dchwebb/Kishoof/Graphics/Kishoof_Front2.jpg

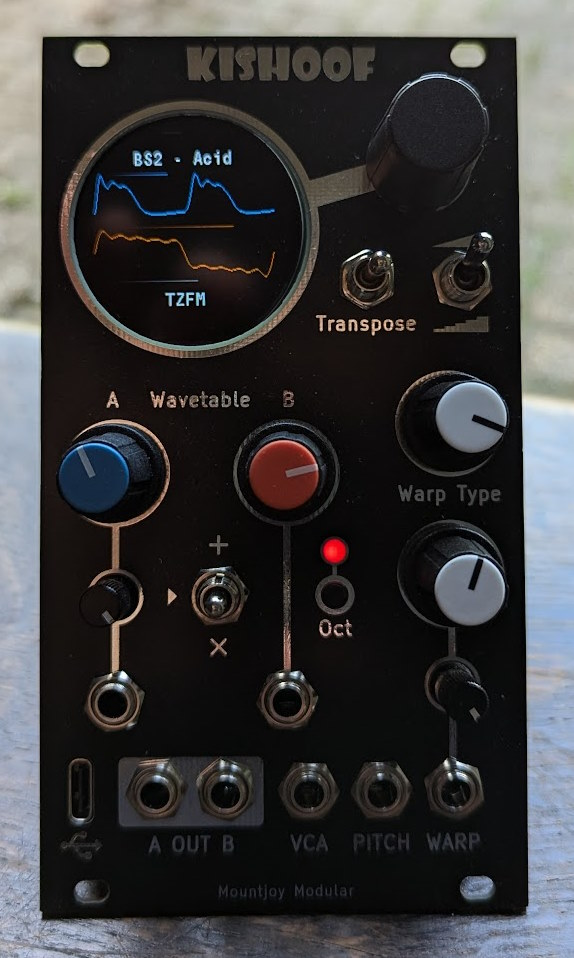
Graphics/Kishoof_Front2.jpg
