dchwebb/Kishoof/Kishoof/src/usb/USB.cpp

#include "USB.h"
#include "GpioPin.h"


USB usb;

extern "C" {
// To enable USB for printf commands (To print floats enable 'Use float with printf from newlib-nano' MCU Build Settings)
size_t _write(int handle, const unsigned char* buf, size_t bufSize)
{
	if (usb.devState == USB::DeviceState::Configured) {
		return usb.SendString(buf, bufSize);
	} else {
		return 0;
	}
}
}

// procedure to allow classes to pass configuration data back via endpoint 1 (eg CDC line setup, MSC MaxLUN etc)
void USB::EP0In(const uint8_t* buff, const uint32_t size)
{
	ep0.inBuffSize = std::min(size, static_cast<uint32_t>(req.Length));
	ep0.inBuff = buff;
	ep0State = EP0State::DataIn;

	USBUpdateDbg({}, {}, {}, ep0.inBuffSize, (uint32_t*)ep0.inBuff);

	EPStartXfer(Direction::in, 0, ep0.inBuffSize);		// sends blank request back
}


void USB::InterruptHandler()					// In Drivers\STM32H7xx_HAL_Driver\Src\stm32h7xx_hal_pcd.c
{
	uint32_t epnum, ep_intr, epint;

	// Handle spurious interrupt
	if ((USB_OTG_HS->GINTSTS & USB_OTG_HS->GINTMSK) == 0) {
		return;
	}

	///////////		10			RXFLVL: RxQLevel Interrupt:  Rx FIFO non-empty Indicates that there is at least one packet pending to be read from the Rx FIFO.
	if (ReadInterrupts(USB_OTG_GINTSTS_RXFLVL))	{
		USB_OTG_HS->GINTMSK &= ~USB_OTG_GINTSTS_RXFLVL;

		const uint32_t receiveStatus = USB_OTG_HS->GRXSTSP;		// OTG status read and pop register: not shown in SFR, but read only (ie do not pop) register under OTG_FS_GLOBAL->FS_GRXSTSR_Device
		epnum = receiveStatus & USB_OTG_GRXSTSP_EPNUM;			// Get the endpoint number
		const uint16_t packetSize = (receiveStatus & USB_OTG_GRXSTSP_BCNT) >> 4;

		USBUpdateDbg(receiveStatus, {}, epnum, packetSize, nullptr);

		if (((receiveStatus & USB_OTG_GRXSTSP_PKTSTS) >> 17) == OutDataReceived && packetSize != 0) {	// 2 = OUT data packet received
			ReadPacket(classByEP[epnum]->outBuff, packetSize, classByEP[epnum]->outBuffOffset);
			USBUpdateDbg({}, {}, {}, {}, classByEP[epnum]->outBuff + classByEP[epnum]->outBuffOffset);
			if (classByEP[epnum]->outBuffPackets > 1) {
				classByEP[epnum]->outBuffOffset += (packetSize / 4);			// When receiving multiple packets increase buffer offset (packet size in bytes -> 32 bit ints)
			}
		} else if (((receiveStatus & USB_OTG_GRXSTSP_PKTSTS) >> 17) == SetupDataReceived) {				// 6 = SETUP data packet received
			ReadPacket(classByEP[epnum]->outBuff, 8U, 0);
			USBUpdateDbg({}, {}, {}, {}, classByEP[epnum]->outBuff);
		} else if (((receiveStatus & USB_OTG_GRXSTSP_PKTSTS) >> 17) == OutTransferCompleted) {			// 3 = transfer completed
			classByEP[epnum]->outBuffOffset = 0;
		}
		if (packetSize != 0) {
			classByEP[epnum]->outBuffCount = packetSize;
		}
		USB_OTG_HS->GINTMSK |= USB_OTG_GINTSTS_RXFLVL;
	}


	/////////// 	80000 		OEPINT OUT endpoint interrupt
	if (ReadInterrupts(USB_OTG_GINTSTS_OEPINT)) {

		// Read the output endpoint interrupt register to ascertain which endpoint(s) fired an interrupt
		ep_intr = ((USBx_DEVICE->DAINT & USBx_DEVICE->DAINTMSK) & USB_OTG_DAINTMSK_OEPM_Msk) >> 16;

		// process each endpoint in turn incrementing the epnum and checking the interrupts (ep_intr) if that endpoint fired
		epnum = 0;
		while (ep_intr != 0) {
			if ((ep_intr & 1) != 0) {
				epint = USBx_OUTEP(epnum)->DOEPINT & USBx_DEVICE->DOEPMSK;

				USBUpdateDbg(epint, {}, epnum, {}, nullptr);

				if ((epint & USB_OTG_DOEPINT_XFRC) == USB_OTG_DOEPINT_XFRC) {		// 0x01 Transfer completed

					USBx_OUTEP(epnum)->DOEPINT = USB_OTG_DOEPINT_XFRC;				// Clear interrupt

					if (epnum == 0) {

						if (devState == DeviceState::Configured && classPendingData) {
							if ((req.RequestType & requestTypeMask) == RequestTypeClass) {
								// Previous OUT interrupt contains instruction (eg host sending CDC LineCoding); next command sends data (Eg LineCoding data)
								classesByInterface[req.Index]->ClassSetupData(req, (uint8_t*)ep0.outBuff);
							}
							classPendingData = false;
							EPStartXfer(Direction::in, 0, 0);
						}

						ep0State = EP0State::Idle;
						USBx_OUTEP(epnum)->DOEPCTL |= USB_OTG_DOEPCTL_STALL;
					} else {
						// Call appropriate data handler depending on endpoint of data
						if (classByEP[epnum]->outBuffPackets <= 1) {
							EPStartXfer(Direction::out, epnum, classByEP[epnum]->outBuffCount);
						}
						classByEP[epnum]->DataOut();
					}
				}

				if ((epint & USB_OTG_DOEPINT_STUP) == USB_OTG_DOEPINT_STUP) {		// SETUP phase done: the application can decode the received SETUP data packet.
					// Parse Setup Request containing data in outBuff filled by RXFLVL interrupt
					req.loadData((uint8_t*)classByEP[epnum]->outBuff);

					USBUpdateDbg({}, req, {}, {}, nullptr);

					ep0State = EP0State::Setup;

					switch (req.RequestType & 0x1F) {		// originally USBD_LL_SetupStage
					case RequestRecipientDevice:
						StdDevReq();
						break;

					case RequestRecipientInterface:
						if ((req.RequestType & requestTypeMask) == RequestTypeClass) {		// 0xA1 & 0x60 == 0x20

							// req.Index holds interface - locate which handler this relates to
							if (req.Length > 0) {
								classesByInterface[req.Index]->ClassSetup(req);
							} else {
								EPStartXfer(Direction::in, 0, 0);
							}
						}
						break;

					case RequestRecipientEndpoint:
						break;

					default:
						CtlError();
						break;
					}

					USBx_OUTEP(epnum)->DOEPINT = USB_OTG_DOEPINT_STUP;				// Clear interrupt
				}

				if ((epint & USB_OTG_DOEPINT_OTEPDIS) == USB_OTG_DOEPINT_OTEPDIS) {	// OUT token received when endpoint disabled
					USBx_OUTEP(epnum)->DOEPINT = USB_OTG_DOEPINT_OTEPDIS;			// Clear interrupt
				}
				if ((epint & USB_OTG_DOEPINT_OTEPSPR) == USB_OTG_DOEPINT_OTEPSPR) {	// Status Phase Received interrupt
					USBx_OUTEP(epnum)->DOEPINT = USB_OTG_DOEPINT_OTEPSPR;			// Clear interrupt
				}
				if ((epint & USB_OTG_DOEPINT_NAK) == USB_OTG_DOEPINT_NAK) {			// 0x2000 OUT NAK interrupt
					USBx_OUTEP(epnum)->DOEPINT = USB_OTG_DOEPINT_NAK;				// Clear interrupt
				}
			}
			epnum++;
			ep_intr >>= 1U;
		}

	}

	///////////		40000 		IEPINT: IN endpoint interrupt
	if (ReadInterrupts(USB_OTG_GINTSTS_IEPINT)) {

		// Read in the device interrupt bits [initially 1]
		ep_intr = (USBx_DEVICE->DAINT & USBx_DEVICE->DAINTMSK) & USB_OTG_DAINTMSK_IEPM_Msk;

		// process each endpoint in turn incrementing the epnum and checking the interrupts (ep_intr) if that endpoint fired
		epnum = 0;
		while (ep_intr != 0) {
			if ((ep_intr & 1) != 0) {

				epint = USBx_INEP(epnum)->DIEPINT & (USBx_DEVICE->DIEPMSK | (((USBx_DEVICE->DIEPEMPMSK >> (epnum & epAddressMask)) & 0x1U) << 7));

				USBUpdateDbg(epint, {}, epnum, {}, nullptr);

				if ((epint & USB_OTG_DIEPINT_XFRC) == USB_OTG_DIEPINT_XFRC) {			// 0x1 Transfer completed interrupt
					uint32_t fifoemptymsk = (0x1UL << (epnum & epAddressMask));
					USBx_DEVICE->DIEPEMPMSK &= ~fifoemptymsk;

					USBx_INEP(epnum)->DIEPINT = USB_OTG_DIEPINT_XFRC;

					if (epnum == 0) {
						if (ep0State == EP0State::DataIn && ep0.inBuffRem == 0) {
							ep0State = EP0State::StatusOut;								// After completing transmission on EP0 send an out packet [HAL_PCD_EP_Receive]
							EPStartXfer(Direction::out, 0, ep_maxPacket);

						} else if (ep0State == EP0State::DataIn && ep0.inBuffRem > 0) {		// For EP0 long packets are sent separately rather than streamed out of the FIFO
							ep0.inBuffSize = ep0.inBuffRem;
							ep0.inBuffRem = 0;
							USBUpdateDbg({}, {}, {}, ep0.inBuffSize, (uint32_t*)ep0.inBuff);

							EPStartXfer(Direction::in, 0, ep0.inBuffSize);
						}
					} else {
						classByEP[epnum]->DataIn();
						classByEP[epnum]->transmitting = false;
					}
				}

				if ((epint & USB_OTG_DIEPINT_TXFE) == USB_OTG_DIEPINT_TXFE) {			// 0x80 Transmit FIFO empty
					USBUpdateDbg({}, {}, {}, classByEP[epnum]->inBuffSize, (uint32_t*)classByEP[epnum]->inBuff);

					if (epnum == 0) {
						if (ep0.inBuffSize > ep_maxPacket) {
							ep0.inBuffRem = classByEP[epnum]->inBuffSize - ep_maxPacket;
							ep0.inBuffSize = ep_maxPacket;
						}

						WritePacket(ep0.inBuff, epnum, ep0.inBuffSize);

						ep0.inBuff += ep0.inBuffSize;		// Move pointer forwards
						const uint32_t fifoemptymsk = 1;
						USBx_DEVICE->DIEPEMPMSK &= ~fifoemptymsk;
					} else {

						// For regular endpoints keep writing packets to the FIFO while space available [PCD_WriteEmptyTxFifo]
						uint16_t len = std::min(classByEP[epnum]->inBuffSize - classByEP[epnum]->inBuffCount, (uint32_t)ep_maxPacket);
						uint16_t len32b = (len + 3) / 4;			// FIFO size is in 4 byte words

						// INEPTFSAV[15:0]: IN endpoint Tx FIFO space available: 0x0: Endpoint Tx FIFO is full; 0x1: 1 31-bit word available; 0xn: n words available
						while (((USBx_INEP(epnum)->DTXFSTS & USB_OTG_DTXFSTS_INEPTFSAV) >= len32b) && (classByEP[epnum]->inBuffCount < classByEP[epnum]->inBuffSize) && (classByEP[epnum]->inBuffSize != 0)) {

							len = std::min(classByEP[epnum]->inBuffSize - classByEP[epnum]->inBuffCount, (uint32_t)ep_maxPacket);
							len32b = (len + 3) / 4;

							WritePacket(classByEP[epnum]->inBuff, epnum, len);

							classByEP[epnum]->inBuff += len;
							classByEP[epnum]->inBuffCount += len;
						}

						if (classByEP[epnum]->inBuffSize <= classByEP[epnum]->inBuffCount) {
							const uint32_t fifoemptymsk = (0x1UL << (epnum & epAddressMask));
							USBx_DEVICE->DIEPEMPMSK &= ~fifoemptymsk;
						}
					}
				}

				if ((epint & USB_OTG_DIEPINT_TOC) == USB_OTG_DIEPINT_TOC) {					// Timeout condition
					USBx_INEP(epnum)->DIEPINT = USB_OTG_DIEPINT_TOC;
				}
				if ((epint & USB_OTG_DIEPINT_ITTXFE) == USB_OTG_DIEPINT_ITTXFE) {			// IN token received when Tx FIFO is empty
					USBx_INEP(epnum)->DIEPINT = USB_OTG_DIEPINT_ITTXFE;
				}
				if ((epint & USB_OTG_DIEPINT_INEPNE) == USB_OTG_DIEPINT_INEPNE) {			// IN endpoint NAK effective
					USBx_INEP(epnum)->DIEPINT = USB_OTG_DIEPINT_INEPNE;
				}
				if ((epint & USB_OTG_DIEPINT_EPDISD) == USB_OTG_DIEPINT_EPDISD) {			// Endpoint disabled interrupt
					USBx_INEP(epnum)->DIEPINT = USB_OTG_DIEPINT_EPDISD;
				}

			}
			epnum++;
			ep_intr >>= 1U;
		}

	}


	/////////// 	800 		USBSUSP: Suspend Interrupt
	if (ReadInterrupts(USB_OTG_GINTSTS_USBSUSP)) {
		if ((USBx_DEVICE->DSTS & USB_OTG_DSTS_SUSPSTS) == USB_OTG_DSTS_SUSPSTS) {
			devState = DeviceState::Suspended;
			USBx_PCGCCTL |= USB_OTG_PCGCCTL_STOPCLK;
		}
		USB_OTG_HS->GINTSTS &= USB_OTG_GINTSTS_USBSUSP;
	}


	/////////// 	1000 		USBRST: Reset Interrupt
	if (ReadInterrupts(USB_OTG_GINTSTS_USBRST))	{
		USBx_DEVICE->DCTL &= ~USB_OTG_DCTL_RWUSIG;

		volatile uint32_t count = 0;
		while (count++ < usbTimeout && (USB_OTG_HS->GRSTCTL & USB_OTG_GRSTCTL_AHBIDL) == 0);		// Wait for AHB master IDLE state.

		count = 0;
		USB_OTG_HS->GRSTCTL = (USB_OTG_GRSTCTL_TXFFLSH | (0x10 << USB_OTG_GRSTCTL_TXFNUM_Pos));			// Flush all TX Fifos
		while (count++ < usbTimeout && (USB_OTG_HS->GRSTCTL & USB_OTG_GRSTCTL_TXFFLSH) == USB_OTG_GRSTCTL_TXFFLSH);

		for (int i = 0; i < 6; i++) {				// FIXME - 6 is number of endpoints (in/out pairs)
			USBx_INEP(i)->DIEPINT = 0xFB7FU;		// see p1177 for explanation: based on datasheet should be more like 0b10100100111011
			USBx_INEP(i)->DIEPCTL &= ~USB_OTG_DIEPCTL_STALL;
			USBx_OUTEP(i)->DOEPINT = 0xFB7FU;
			USBx_OUTEP(i)->DOEPCTL &= ~USB_OTG_DOEPCTL_STALL;
			USBx_OUTEP(i)->DOEPCTL |= USB_OTG_DOEPCTL_SNAK;
		}
		USBx_DEVICE->DAINTMSK |= 0x10001U;

		USBx_DEVICE->DOEPMSK |= USB_OTG_DOEPMSK_STUPM | USB_OTG_DOEPMSK_XFRCM | USB_OTG_DOEPMSK_EPDM | USB_OTG_DOEPMSK_OTEPSPRM;
		USBx_DEVICE->DIEPMSK |= USB_OTG_DIEPMSK_TOM | USB_OTG_DIEPMSK_XFRCM | USB_OTG_DIEPMSK_EPDM;

		// Clear Default Address (will be set later when address instruction received from host)
		USBx_DEVICE->DCFG &= ~USB_OTG_DCFG_DAD;

		// Set up EP0 to receive SETUP packets
		// Set PKTCNT to 1, XFRSIZ to 24, STUPCNT to 3 (number of back-to-back SETUP data packets endpoint can receive)
		if ((USBx_OUTEP(0U)->DOEPCTL & USB_OTG_DOEPCTL_EPENA) != USB_OTG_DOEPCTL_EPENA) {
			USBx_OUTEP(0U)->DOEPTSIZ = (1U << 19) | (3U * 8U) | USB_OTG_DOEPTSIZ_STUPCNT;
		}

		USB_OTG_HS->GINTSTS &= USB_OTG_GINTSTS_USBRST;
	}


	/////////// 	2000		ENUMDNE: Enumeration done Interrupt
	if (ReadInterrupts(USB_OTG_GINTSTS_ENUMDNE)) {
		// Set the Maximum packet size of the IN EP based on the enumeration speed
		USBx_INEP(0U)->DIEPCTL &= ~USB_OTG_DIEPCTL_MPSIZ;
		USBx_DEVICE->DCTL |= USB_OTG_DCTL_CGINAK;		//  Clear global IN NAK

		// Assuming Full Speed USB and clock > 32MHz Set USB Turnaround time
		USB_OTG_HS->GUSBCFG &= ~USB_OTG_GUSBCFG_TRDT;
		USB_OTG_HS->GUSBCFG |= (6 << 10);

		ActivateEndpoint(0, Direction::out, Control);			// Open EP0 OUT
		ActivateEndpoint(0, Direction::in, Control);			// Open EP0 IN

		ep0State = EP0State::Idle;

		USB_OTG_HS->GINTSTS &= USB_OTG_GINTSTS_ENUMDNE;
	}


	///////////		40000000	SRQINT: Connection event Interrupt
	if (ReadInterrupts(USB_OTG_GINTSTS_SRQINT))	{
		USB_OTG_HS->GINTSTS &= USB_OTG_GINTSTS_SRQINT;
	}


	/////////// 	80000000	WKUINT: Resume Interrupt
	if (ReadInterrupts(USB_OTG_GINTSTS_WKUINT)) {
		USBx_DEVICE->DCTL &= ~USB_OTG_DCTL_RWUSIG;				// Clear the Remote Wake-up Signaling

		if (devState == DeviceState::Suspended) {
			devState = DeviceState::Default;
		}

		USB_OTG_HS->GINTSTS &= USB_OTG_GINTSTS_WKUINT;
	}


	/////////// OTGINT: Handle Disconnection event Interrupt
	if (ReadInterrupts(USB_OTG_GINTSTS_OTGINT)) {
		uint32_t temp = USB_OTG_HS->GOTGINT;

		if ((temp & USB_OTG_GOTGINT_SEDET) == USB_OTG_GOTGINT_SEDET) {
			devState = DeviceState::Default;

			Init(true);
		}

		USB_OTG_HS->GOTGINT |= temp;
	}

}


void USB::Init(bool softReset)
{
	volatile uint32_t count = 0;

	if (!softReset) {
#if (USB_DEBUG)
		uart.Init();
#endif
		RCC->CR |= RCC_CR_HSI48ON;						// Enable Internal High Speed oscillator for USB
		while (count++ < usbTimeout && (RCC->CR & RCC_CR_HSI48RDY) == 0);		// Wait till internal USB oscillator is ready
		RCC->CDCCIP2R |= RCC_CDCCIP2R_USBSEL;			// Set the USB CLock MUX to RC48
		PWR->CR3 |= PWR_CR3_USB33DEN;					// Enable VDD33USB supply level detector

		GpioPin::Init(GPIOA, 9, GpioPin::Type::Input);						// PA9: USB_OTG_HS_VBUS
		GpioPin::Init(GPIOA, 11, GpioPin::Type::AlternateFunction, 10);		// PA11: USB_OTG_HS_DM
		GpioPin::Init(GPIOA, 12, GpioPin::Type::AlternateFunction, 10);		// PA12: USB_OTG_HS_DP

		RCC->AHB1ENR |= RCC_AHB1ENR_USB1OTGHSEN;		// USB2OTG (OTG_HS1) Peripheral Clocks Enable

		NVIC_SetPriority(OTG_HS_IRQn, 2);
		NVIC_EnableIRQ(OTG_HS_IRQn);
	}

	USB_OTG_HS->GAHBCFG &= ~USB_OTG_GAHBCFG_GINT;		// Disable the controller's Global Int in the AHB Config reg
	USB_OTG_HS->GUSBCFG |= USB_OTG_GUSBCFG_PHYSEL;		// Select FS Embedded PHY

	// Reset the core (needed after clock change) - NB removed delays
	count = 0;
	while (count++ < 0xF000000 && (USB_OTG_HS->GRSTCTL & USB_OTG_GRSTCTL_AHBIDL) == 0);		// Wait for AHB master IDLE state.
	USB_OTG_HS->GRSTCTL |= USB_OTG_GRSTCTL_CSRST;
	count = 0;
	while (count++ < 0xF000000 && ((USB_OTG_HS->GRSTCTL & USB_OTG_GRSTCTL_CSRST) == USB_OTG_GRSTCTL_CSRST));

	USB_OTG_HS->GCCFG |= USB_OTG_GCCFG_PWRDWN;			// Activate the transceiver in transmission/reception. When reset, the transceiver is kept in power-down. 0 = USB FS transceiver disabled; 1 = USB FS transceiver enabled
	USB_OTG_HS->GUSBCFG |= USB_OTG_GUSBCFG_FDMOD;		// Force USB device mode

	count = 0;
	while (count++ < 0xF000000 && (USB_OTG_HS->GINTSTS & USB_OTG_GINTSTS_CMOD));	// CMOD = 0 is device mode

	// Clear all transmit FIFO address and data lengths - these will be set to correct values below for endpoints 0,1 and 2
	for (uint8_t i = 0; i < 15; ++i) {
		USB_OTG_HS->DIEPTXF[i] = 0U;
	}

	USB_OTG_HS->GCCFG |= USB_OTG_GCCFG_VBDEN; 			// Enable HW VBUS sensing
	USBx_PCGCCTL = 0U;									// Restart the Phy Clock

	USBx_DEVICE->DCFG |= USB_OTG_DCFG_DSPD;				// 11: Full speed using internal FS PHY

	USB_OTG_HS->GRSTCTL |= USB_OTG_GRSTCTL_TXFNUM_4;	// Select buffers to flush. 10000: Flush all the transmit FIFOs in device or host mode
	USB_OTG_HS->GRSTCTL |= USB_OTG_GRSTCTL_TXFFLSH;		// Flush the TX buffers
	count = 0;
	while (count++ < 0xF000000 && ((USB_OTG_HS->GRSTCTL & USB_OTG_GRSTCTL_TXFFLSH) == USB_OTG_GRSTCTL_TXFFLSH));

	USB_OTG_HS->GRSTCTL = USB_OTG_GRSTCTL_RXFFLSH;		// Flush the RX buffers
	count = 0;
	while (count++ < 0xF000000 && ((USB_OTG_HS->GRSTCTL & USB_OTG_GRSTCTL_RXFFLSH) == USB_OTG_GRSTCTL_RXFFLSH));

	// Clear all pending Device Interrupts
	USBx_DEVICE->DIEPMSK = 0U;
	USBx_DEVICE->DOEPMSK = 0U;
	USBx_DEVICE->DAINTMSK = 0U;

	USB_OTG_HS->GINTSTS = 0xBFFFFFFFU;					// Clear pending interrupts (except SRQINT Session request/new session detected)

	// Enable interrupts
	USB_OTG_HS->GINTMSK = 0U;							// Disable all interrupts
	USB_OTG_HS->GINTMSK |= USB_OTG_GINTMSK_RXFLVLM | USB_OTG_GINTMSK_USBSUSPM |			// Receive FIFO non-empty mask; USB suspend
			USB_OTG_GINTMSK_USBRST | USB_OTG_GINTMSK_ENUMDNEM |							// USB reset; Enumeration done
			USB_OTG_GINTMSK_IEPINT | USB_OTG_GINTMSK_OEPINT | USB_OTG_GINTMSK_WUIM |	// IN endpoint; OUT endpoint; Resume/remote wakeup detected
			USB_OTG_GINTMSK_SRQIM | USB_OTG_GINTMSK_OTGINT;								// Session request/new session detected; OTG interrupt [both used for VBUS sensing]


	// NB - FIFO Sizes are in words NOT bytes. There is a total size of 1024 (1024x4 = 4096 bytes) available which is divided up thus:
	// FIFO		Start		Size
	// RX 		0			128
	// EP0 TX	128			64
	// EP1 TX	192			64
	// EP2 TX 	256			64
	// EP3 TX 	320			64

	USB_OTG_HS->GRXFSIZ = 128;		 									// Rx FIFO depth

	// Endpoint 0 Transmit FIFO size/address (as in device mode - this is also used as the non-periodic transmit FIFO size in host mode)
	USB_OTG_HS->DIEPTXF0_HNPTXFSIZ = (64 << USB_OTG_TX0FD_Pos) |		// IN Endpoint 0 Tx FIFO depth
			(128 << USB_OTG_TX0FSA_Pos);								// IN Endpoint 0 FIFO transmit RAM start address - this is offset from the RX FIFO (set above to 128)

	// Endpoint 1 FIFO size/address (address is offset from EP0 address+size above)
	USB_OTG_HS->DIEPTXF[0] = (64 << USB_OTG_DIEPTXF_INEPTXFD_Pos) |		// IN endpoint 1 Tx FIFO depth
			(192 << USB_OTG_DIEPTXF_INEPTXSA_Pos);  					// IN endpoint 1 FIFO transmit RAM start address

	// Endpoint 2 FIFO size/address (address is offset from EP1 address+size above)
	USB_OTG_HS->DIEPTXF[1] = (64 << USB_OTG_DIEPTXF_INEPTXFD_Pos) |		// IN endpoint 2 Tx FIFO depth
			(256 << USB_OTG_DIEPTXF_INEPTXSA_Pos);  					// IN endpoint 2 FIFO transmit RAM start address

	// Endpoint 3 FIFO size/address (address is offset from EP2 address+size above)
	USB_OTG_HS->DIEPTXF[2] = (64 << USB_OTG_DIEPTXF_INEPTXFD_Pos) |		// IN endpoint 3 Tx FIFO depth
			(320 << USB_OTG_DIEPTXF_INEPTXSA_Pos);  					// IN endpoint 3 FIFO transmit RAM start address

	// In case phy is stopped, ensure to ungate and restore the phy CLK
	USBx_PCGCCTL &= ~(USB_OTG_PCGCCTL_STOPCLK | USB_OTG_PCGCCTL_GATECLK);
	USBx_DEVICE->DCTL |= USB_OTG_DCTL_SDIS;

	USB_OTG_HS->GAHBCFG |= USB_OTG_GAHBCFG_GINT;						// Activate USB Interrupts
	USBx_DEVICE->DCTL &= ~USB_OTG_DCTL_SDIS;							// Activate USB
}


void USB::ActivateEndpoint(uint8_t endpoint, const Direction direction, const EndPointType eptype)
{
	endpoint = endpoint & 0xF;

	if (direction == Direction::in) {
		USBx_DEVICE->DAINTMSK |= USB_OTG_DAINTMSK_IEPM & (1 << endpoint);

		if ((USBx_INEP(endpoint)->DIEPCTL & USB_OTG_DIEPCTL_USBAEP) == 0) {
			USBx_INEP(endpoint)->DIEPCTL |=
					(ep_maxPacket & USB_OTG_DIEPCTL_MPSIZ) |
					((uint32_t)eptype << USB_OTG_DIEPCTL_EPTYP_Pos) |
					(endpoint << USB_OTG_DIEPCTL_TXFNUM_Pos) |
					USB_OTG_DIEPCTL_USBAEP;
		}
	} else {
		USBx_DEVICE->DAINTMSK |= USB_OTG_DAINTMSK_OEPM & ((1 << endpoint) << USB_OTG_DAINTMSK_OEPM_Pos);

		if (((USBx_OUTEP(endpoint)->DOEPCTL) & USB_OTG_DOEPCTL_USBAEP) == 0) {
			USBx_OUTEP(endpoint)->DOEPCTL |=
					(ep_maxPacket & USB_OTG_DOEPCTL_MPSIZ) |
					((uint32_t)eptype << USB_OTG_DOEPCTL_EPTYP_Pos) |
					USB_OTG_DOEPCTL_USBAEP;
		}
	}
}


void USB::DeactivateEndpoint(uint8_t endpoint, const Direction direction)
{
	endpoint = endpoint & 0xF;

	if (direction == Direction::in) {
		if ((USBx_INEP(endpoint)->DIEPCTL & USB_OTG_DIEPCTL_EPENA) == USB_OTG_DIEPCTL_EPENA) {
			USBx_INEP(endpoint)->DIEPCTL |= USB_OTG_DIEPCTL_SNAK;
			USBx_INEP(endpoint)->DIEPCTL |= USB_OTG_DIEPCTL_EPDIS;
		}

		USBx_DEVICE->DEACHMSK &= ~(USB_OTG_DAINTMSK_IEPM & (uint32_t)(1 << (endpoint)));
		USBx_DEVICE->DAINTMSK &= ~(USB_OTG_DAINTMSK_IEPM & (uint32_t)(1 << (endpoint)));
		USBx_INEP(endpoint)->DIEPCTL &= ~(USB_OTG_DIEPCTL_USBAEP |
				USB_OTG_DIEPCTL_MPSIZ |
				USB_OTG_DIEPCTL_TXFNUM |
				USB_OTG_DIEPCTL_SD0PID_SEVNFRM |
				USB_OTG_DIEPCTL_EPTYP);
	} else {
		if ((USBx_OUTEP(endpoint)->DOEPCTL & USB_OTG_DOEPCTL_EPENA) == USB_OTG_DOEPCTL_EPENA) {
			USBx_OUTEP(endpoint)->DOEPCTL |= USB_OTG_DOEPCTL_SNAK;
			USBx_OUTEP(endpoint)->DOEPCTL |= USB_OTG_DOEPCTL_EPDIS;
		}

		USBx_DEVICE->DEACHMSK &= ~(USB_OTG_DAINTMSK_OEPM & ((uint32_t)(1UL << endpoint) << USB_OTG_DAINTMSK_OEPM_Pos));
		USBx_DEVICE->DAINTMSK &= ~(USB_OTG_DAINTMSK_OEPM & ((uint32_t)(1UL << endpoint) << USB_OTG_DAINTMSK_OEPM_Pos));
		USBx_OUTEP(endpoint)->DOEPCTL &= ~(USB_OTG_DOEPCTL_USBAEP |
				USB_OTG_DOEPCTL_MPSIZ |
				USB_OTG_DOEPCTL_SD0PID_SEVNFRM |
				USB_OTG_DOEPCTL_EPTYP);
	}
}


void USB::ReadPacket(const uint32_t* dest, const uint16_t len, const uint32_t offset)
{
	// Read a packet from the RX FIFO
	uint32_t* pDest = (uint32_t*)dest + offset;
	const uint32_t count32b = ((uint32_t)len + 3U) / 4U;

	for (uint32_t i = 0; i < count32b; i++)	{
		*pDest = USBx_DFIFO(0);
		pDest++;
	}
}


void USB::WritePacket(const uint8_t* src, const uint8_t endpoint, const uint32_t len)
{
	uint32_t* pSrc = (uint32_t*)src;
	const uint32_t count32b = ((uint32_t)len + 3U) / 4U;

	for (uint32_t i = 0; i < count32b; i++) {
		USBx_DFIFO(endpoint) = *pSrc;
		pSrc++;
	}
}


// Descriptors in usbd_desc.c
void USB::GetDescriptor()
{
	uint32_t strSize;

	switch (req.Value >> 8)	{
	case DeviceDescriptor:
		return EP0In(deviceDescr, sizeof(deviceDescr));
		break;

	case ConfigurationDescriptor:
		return EP0In(configDescriptor, MakeConfigDescriptor());		// Construct config descriptor from individual classes
		break;

	case BosDescriptor:
		return EP0In(bosDescr, sizeof(bosDescr));
		break;

	case DeviceQualifierDescriptor:
		return EP0In(deviceQualifierDescr, sizeof(deviceQualifierDescr));
		break;

	case StringDescriptor:

		switch ((uint8_t)(req.Value)) {
		case StringIndex::LangId:				// 300
			return EP0In(langIDDescr, sizeof(langIDDescr));
			break;

		case StringIndex::Manufacturer:			// 301
			strSize = StringToUnicode(USBD_MANUFACTURER_STRING, stringDescr);
			return EP0In(stringDescr, strSize);
			break;

		case StringIndex::Product:				// 302
			strSize = StringToUnicode(USBD_PRODUCT_STRING, stringDescr);
			return EP0In(stringDescr, strSize);
			break;

		case StringIndex::Serial:				// 303
			SerialToUnicode();
			return EP0In(stringDescr, stringDescr[0]);				// length is 24 bytes (x2 for unicode padding) + 2 for header
			break;

		case StringIndex::Configuration:		// 304
	    	strSize = StringToUnicode(USBD_CFG_STRING, stringDescr);
	    	return EP0In(stringDescr, strSize);
	    	break;

	    case StringIndex::MassStorageClass:		// 305
	    	strSize = StringToUnicode(USBD_MSC_STRING, stringDescr);
	    	return EP0In(stringDescr, strSize);
			break;

	    case StringIndex::CommunicationClass:	// 306
	    	strSize = StringToUnicode(USBD_CDC_STRING, stringDescr);
	    	return EP0In(stringDescr, strSize);
			break;

	    case StringIndex::AudioClass:			// 307
	    	strSize = StringToUnicode(USBD_MIDI_STRING, stringDescr);
	    	return EP0In(stringDescr, strSize);
			break;

		default:
			CtlError();
			return;
		}
		break;

		default:
			CtlError();
			return;
	}

	if (req.Length == 0) {
		EPStartXfer(Direction::in, 0, 0);			// FIXME - this never seems to happen
	}
}


uint32_t USB::MakeConfigDescriptor()
{
	// Construct the configuration descriptor from the various class descriptors with header
	static constexpr uint8_t descrHeaderSize = 9;
	uint32_t descPos = descrHeaderSize;
	for (auto c : classByEP) {
		if (c != nullptr) {
			const uint8_t* descBuff = nullptr;
			uint32_t descSize = c->GetInterfaceDescriptor(&descBuff);
			memcpy(&configDescriptor[descPos], descBuff, descSize);
			descPos += descSize;
		}
	}

	// Insert config descriptor header
	const uint8_t descriptorHeader[] = {
		0x09,								// bLength: Configuration Descriptor size
		ConfigurationDescriptor,			// bDescriptorType: Configuration
		LOBYTE(descPos),					// wTotalLength
		HIBYTE(descPos),
		interfaceCount,						// bNumInterfaces: 5 [1 MSC, 2 CDC, 2 MIDI]
		0x01,								// bConfigurationValue: Configuration value
		0x04,								// iConfiguration: Index of string descriptor describing the configuration
		0xC0,								// bmAttributes: self powered
		0x32,								// MaxPower 0 mA
	};
	memcpy(&configDescriptor[0], descriptorHeader, descrHeaderSize);

	return descPos;
}


uint32_t USB::StringToUnicode(const std::string_view desc, uint8_t *unicode)
{
	uint32_t idx = 2;
	for (auto c: desc) {
		unicode[idx++] = c;
		unicode[idx++] = 0;
	}
	unicode[0] = idx;
	unicode[1] = StringDescriptor;

	return idx;
}


void USB::SerialToUnicode()
{
	const uint32_t* uidAddr = (uint32_t*)UID_BASE;			// Location in memory that holds 96 bit Unique device ID register

	char uidBuff[usbSerialNoSize + 1];
	snprintf(uidBuff, usbSerialNoSize + 1, "%08lx%08lx%08lx", uidAddr[0], uidAddr[1], uidAddr[2]);

	stringDescr[0] = usbSerialNoSize * 2 + 2;				// length is 24 bytes (x2 for unicode padding) + 2 for header
	stringDescr[1] = StringDescriptor;
	for (uint8_t i = 0; i < usbSerialNoSize; ++i) {
		//const uint8_t sumUid = uidAddr[i] + uidAddr[i + 12];
		stringDescr[i * 2 + 2] = uidBuff[i];
	}
}


void USB::StdDevReq()
{
	uint8_t dev_addr;
	switch (req.RequestType & requestTypeMask)
	{
	case RequestTypeClass:
	case RequestTypeVendor:
		// pdev->pClass->Setup(pdev, req);
		break;

	case RequestTypeStandard:

		switch (static_cast<Request>(req.Request))
		{
		case Request::GetDescriptor:
			GetDescriptor();
			break;

		case Request::SetAddress:
			dev_addr = (uint8_t)(req.Value) & 0x7FU;
			USBx_DEVICE->DCFG &= ~(USB_OTG_DCFG_DAD);
			USBx_DEVICE->DCFG |= ((uint32_t)dev_addr << 4) & USB_OTG_DCFG_DAD;
			ep0State = EP0State::StatusIn;
			EPStartXfer(Direction::in, 0, 0);
			devState = DeviceState::Addressed;
			break;

		case Request::SetConfiguration:
			if (devState == DeviceState::Addressed) {
				devState = DeviceState::Configured;

				for (auto c : classByEP) {
					c->ActivateEP();
				}

				ep0State = EP0State::StatusIn;
				EPStartXfer(Direction::in, 0, 0);
			}
			break;

		default:
			CtlError();
			break;
		}
		break;

		default:
			CtlError();
			break;
	}

}


void USB::EPStartXfer(const Direction direction, uint8_t endpoint, uint32_t xfer_len) {

	if (direction == Direction::in) {

		endpoint = endpoint & epAddressMask;					// Strip out 0x80 if endpoint passed eg as 0x81

		if (endpoint == 0 && xfer_len > ep_maxPacket) {		// If the transfer is larger than the maximum packet size send the maximum size and use the remaining flag to trigger a second send
			ep0.inBuffRem = xfer_len - ep_maxPacket;
			xfer_len = ep_maxPacket;
		}

		USBx_INEP(endpoint)->DIEPTSIZ &= ~(USB_OTG_DIEPTSIZ_XFRSIZ | USB_OTG_DIEPTSIZ_PKTCNT);

		USBx_INEP(endpoint)->DIEPTSIZ |= (USB_OTG_DIEPTSIZ_PKTCNT & (((xfer_len + ep_maxPacket - 1) / ep_maxPacket) << USB_OTG_DIEPTSIZ_PKTCNT_Pos));
		USBx_INEP(endpoint)->DIEPTSIZ |= (USB_OTG_DIEPTSIZ_XFRSIZ & xfer_len);

		USBx_INEP(endpoint)->DIEPCTL |= (USB_OTG_DIEPCTL_CNAK | USB_OTG_DIEPCTL_EPENA);		// EP enable, IN data in FIFO

		if (xfer_len > 0) {
			USBx_DEVICE->DIEPEMPMSK |= 1UL << endpoint;		// Enable the Tx FIFO Empty Interrupt for this EP
		}
	} else { 		// OUT endpoint

		classByEP[endpoint]->outBuffPackets = 1;
		classByEP[endpoint]->outBuffOffset = 0;

		// If the transfer is larger than the maximum packet size send the total size and number of packets calculated from the end point maximum packet size
		if (xfer_len > ep_maxPacket) {
			classByEP[endpoint]->outBuffPackets = (xfer_len + ep_maxPacket - 1U) / ep_maxPacket;
		}

		USBx_OUTEP(endpoint)->DOEPTSIZ &= ~(USB_OTG_DOEPTSIZ_XFRSIZ | USB_OTG_DOEPTSIZ_PKTCNT);

		USBx_OUTEP(endpoint)->DOEPTSIZ |= (USB_OTG_DOEPTSIZ_PKTCNT & (classByEP[endpoint]->outBuffPackets << USB_OTG_DOEPTSIZ_PKTCNT_Pos));
		USBx_OUTEP(endpoint)->DOEPTSIZ |= (USB_OTG_DOEPTSIZ_XFRSIZ & xfer_len);

		USBx_OUTEP(endpoint)->DOEPCTL |= (USB_OTG_DOEPCTL_CNAK | USB_OTG_DOEPCTL_EPENA);		// EP enable
	}
}


void USB::CtlError()
{
	USBx_INEP(0)->DIEPCTL |= USB_OTG_DIEPCTL_STALL;
	USBx_OUTEP(0)->DOEPCTL |= USB_OTG_DOEPCTL_STALL;

	// Set PKTCNT to 1, XFRSIZ to 24, STUPCNT to 3 (number of back-to-back SETUP data packets endpoint can receive)
	//USBx_OUTEP(0U)->DOEPTSIZ = (1U << 19) | (3U * 8U) | USB_OTG_DOEPTSIZ_STUPCNT;
}


bool USB::ReadInterrupts(const uint32_t interrupt)
{
#if (USB_DEBUG)
	if (((USB_OTG_HS->GINTSTS & USB_OTG_HS->GINTMSK) & interrupt) == interrupt) {
		usbDebug[usbDebugEvent & usbDebugMask].eventNo = usbDebugEvent;
		usbDebug[usbDebugEvent & usbDebugMask].Interrupt = USB_OTG_HS->GINTSTS & USB_OTG_HS->GINTMSK;
		usbDebugEvent++;
	}
#endif

	return ((USB_OTG_HS->GINTSTS & USB_OTG_HS->GINTMSK) & interrupt) == interrupt;
}


void USB::PauseEndpoint(USBHandler& handler)
{
	USBx_INEP(handler.inEP & 0xF)->DIEPCTL |= USB_OTG_DIEPCTL_SNAK;
	USBx_OUTEP(handler.outEP)->DOEPCTL |= USB_OTG_DOEPCTL_SNAK;
	DelayMS(2);
}


void USB::ResumeEndpoint(USBHandler& handler)
{
	USBx_INEP(handler.inEP & 0xF)->DIEPCTL |= USB_OTG_DIEPCTL_CNAK;
	USBx_OUTEP(handler.outEP)->DOEPCTL |= USB_OTG_DOEPCTL_CNAK;
}


size_t USB::SendData(const uint8_t* data, const uint16_t len, uint8_t endpoint)
{
	endpoint &= epAddressMask;
	if (devState == DeviceState::Configured && !classByEP[endpoint]->transmitting) {
		classByEP[endpoint]->transmitting = true;
		classByEP[endpoint]->inBuff = data;
		classByEP[endpoint]->inBuffSize = len;
		classByEP[endpoint]->inBuffCount = 0;
		ep0State = EP0State::DataIn;
		EPStartXfer(Direction::in, endpoint, len);
		return len;
	} else {
		return 0;
	}
}


void USB::SendString(const char* s)
{
	uint16_t counter = 0;
	while (cdc.transmitting && counter < 10000) {
		++counter;
	}
	SendData((uint8_t*)s, strlen(s), CDC_In);
}


void USB::SendString(const std::string s)
{
	SendString(s.c_str());
}


size_t USB::SendString(const unsigned char* s, size_t len)
{
	uint16_t counter = 0;
	while (cdc.transmitting && counter < 10000) {
		++counter;
	}
	return SendData((uint8_t*)s, len, CDC_In);
}


#if (USB_DEBUG)

#include <string>

std::string IntToString(const int32_t& v) {
	return std::to_string(v);
}

std::string HexToString(const uint32_t& v, const bool& spaces) {
	char buf[20];
	if (spaces) {
		if (v != 0) {
			uint8_t* bytes = (uint8_t*)&v;
			sprintf(buf, "%02X%02X%02X%02X", bytes[0], bytes[1], bytes[2], bytes[3]);
		} else {
			sprintf(buf, " ");
		}
	} else {
		sprintf(buf, "%X", (unsigned int)v);
	}
	return std::string(buf);

}

std::string HexByte(const uint16_t& v) {
	char buf[50];
	sprintf(buf, "%X", v);
	return std::string(buf);

}


void USB::OutputDebug()
{
	uart.SendString("Event,Interrupt,Desc,Int Data,Desc,Endpoint,mRequest,Request,Value,Index,Length,PacketSize,XferBuff\n");
	std::string interrupt, subtype;

	for (uint32_t i = 0; i < usbDebugCount; ++i) {

		const uint16_t evNo = (usbDebugEvent + i) & usbDebugMask;

		subtype = "";

		switch (usbDebug[evNo].Interrupt) {
		case USB_OTG_GINTSTS_RXFLVL:
			interrupt = "RXFLVL";

			switch ((usbDebug[evNo].IntData & USB_OTG_GRXSTSP_PKTSTS) >> 17) {
				case OutDataReceived:			subtype = "Out packet rec";			break;		// 2 = OUT data packet received
				case OutTransferCompleted:		subtype = "Transfer completed";		break;		// 3 = Transfer completed
				case SetupDataReceived:			subtype = "Setup packet rec";		break;		// 6 = SETUP data packet received
				case SetupTransComplete:		subtype = "Setup comp";				break;		// 4 = SETUP comp
				default:						subtype = "";
			}

			break;
		case USB_OTG_GINTSTS_SRQINT:		interrupt = "SRQINT";			break;		// 0x40000000
		case USB_OTG_GINTSTS_USBSUSP:		interrupt = "USBSUSP";			break;		// 0x800
		case USB_OTG_GINTSTS_WKUINT:		interrupt = "WKUINT";			break;		// 0x80000000
		case USB_OTG_GINTSTS_USBRST:		interrupt = "USBRST";			break;		// 0x1000
		case USB_OTG_GINTSTS_ENUMDNE:		interrupt = "ENUMDNE";			break;		// 0x2000
		case USB_OTG_GINTSTS_OEPINT:		interrupt = "OEPINT";						// 0x80000

			switch (usbDebug[evNo].IntData) {
			case USB_OTG_DOEPINT_XFRC:			subtype = "Transfer Done";							break;

			case USB_OTG_DOEPINT_STUP:

				switch (usbDebug[evNo].Request.Value >> 8)	{
					case DeviceDescriptor:			subtype = "Device Descriptor";					break;
					case ConfigurationDescriptor:	subtype = "Configuration Descriptor";			break;
					case BosDescriptor:				subtype = "Bos Descriptor";						break;
					case DeviceQualifierDescriptor:	subtype = "Device Qualifier Descriptor";		break;
					case StringDescriptor:

						switch ((uint8_t)(usbDebug[evNo].Request.Value)) {
							case StringIndex::LangId:				subtype = "Lang Id";			break;
							case StringIndex::Manufacturer:			subtype = "Manufacturer";		break;
							case StringIndex::Product:				subtype = "Product";			break;
							case StringIndex::Serial:				subtype = "Serial";				break;
							case StringIndex::Configuration:		subtype = "Configuration";		break;
							case StringIndex::MassStorageClass:		subtype = "MassStorageClass";	break;
							case StringIndex::CommunicationClass:	subtype = "CommunicationClass";	break;
							case StringIndex::AudioClass:			subtype = "AudioClass";			break;
							default:				    			subtype = "Setup phase done";	break;
						}
						break;

					default: 									subtype = "Setup phase done";	break;
				}

				break;

			default:
				subtype = "";
			}
			break;

		case USB_OTG_GINTSTS_IEPINT:		// 0x40000
			interrupt = "IEPINT";

			switch (usbDebug[evNo].IntData) {
				case USB_OTG_DIEPINT_XFRC:			subtype = "Transfer completed";			break;
				case USB_OTG_DIEPINT_TXFE:			subtype = "Transmit FIFO empty";		break;
				default:							subtype = "";
			}
			break;

		default:
			interrupt = "";
		}

		if (usbDebug[evNo].Interrupt != 0) {
			uart.SendString(IntToString(usbDebug[evNo].eventNo) + ","
					+ HexToString(usbDebug[evNo].Interrupt, false) + "," + interrupt + ","
					+ HexToString(usbDebug[evNo].IntData, false) + "," + subtype + ","
					+ IntToString(usbDebug[evNo].endpoint) + ","
					+ HexByte(usbDebug[evNo].Request.RequestType) + ", "
					+ HexByte(usbDebug[evNo].Request.Request) + ", "
					+ HexByte(usbDebug[evNo].Request.Value) + ", "
					+ HexByte(usbDebug[evNo].Request.Index) + ", "
					+ HexByte(usbDebug[evNo].Request.Length) + ", "
					+ IntToString(usbDebug[evNo].PacketSize) + ", "
					+ HexToString(usbDebug[evNo].xferBuff[0], true) + " "
					+ HexToString(usbDebug[evNo].xferBuff[1], true) + " "
					+ HexToString(usbDebug[evNo].xferBuff[2], true) + " "
					+ HexToString(usbDebug[evNo].xferBuff[3], true) + "\n");
		}
	}

}


/*
startup sequence:
Event,Interrupt,Desc,Int Data,Desc,Endpoint,mRequest,Request,Value,Index,Length,Scsi,PacketSize,XferBuff
0,40000000,SRQINT,0,,0,0, 0, 0, 0, 0, 0, 0,
1,800,USBSUSP,0,,0,0, 0, 0, 0, 0, 0, 0,
2,1000,USBRST,0,,0,0, 0, 0, 0, 0, 0, 0,
3,2000,ENUMDNE,0,,0,0, 0, 0, 0, 0, 0, 0,
4,10,RXFLVL,8C0080,Setup packet rec,0,0, 0, 0, 0, 0, 0, 8, 80060001 00004000
5,10,RXFLVL,880000,Setup comp,0,0, 0, 0, 0, 0, 0, 0,
6,80000,OEPINT,8,Setup phase done,0,80, 6, 100, 0, 40, 0, 18, 12010102 EF020140 83042A57 00020102
7,40000,IEPINT,80,Transmit FIFO empty,0,0, 0, 0, 0, 0, 0, 18, 12010102 EF020140 83042A57 00020102
8,40000,IEPINT,1,Transfer completed,0,0, 0, 0, 0, 0, 0, 0,
9,10,RXFLVL,A50000,Out packet rec,0,0, 0, 0, 0, 0, 0, 0,
10,10,RXFLVL,A70000,Transfer completed,0,0, 0, 0, 0, 0, 0, 0,
11,80000,OEPINT,1,Transfer completed,0,0, 0, 0, 0, 0, 0, 0,
12,10,RXFLVL,AC0080,Setup packet rec,0,0, 0, 0, 0, 0, 0, 8, 00052A00
13,10,RXFLVL,A80000,Setup comp,0,0, 0, 0, 0, 0, 0, 0,
14,80000,OEPINT,8,Setup phase done,0,0, 5, 2A, 0, 0, 0, 0,
15,10,RXFLVL,1EC0080,Setup packet rec,0,0, 0, 0, 0, 0, 0, 8, 80060001 00001200
16,10,RXFLVL,1E80000,Setup comp,0,0, 0, 0, 0, 0, 0, 0,
17,80000,OEPINT,8,Setup phase done,0,80, 6, 100, 0, 12, 0, 18, 12010102 EF020140 83042A57 00020102
18,40000,IEPINT,80,Transmit FIFO empty,0,0, 0, 0, 0, 0, 0, 18, 12010102 EF020140 83042A57 00020102
19,40000,IEPINT,1,Transfer completed,0,0, 0, 0, 0, 0, 0, 0,
20,10,RXFLVL,50000,Out packet rec,0,0, 0, 0, 0, 0, 0, 0,
21,10,RXFLVL,70000,Transfer completed,0,0, 0, 0, 0, 0, 0, 0,
22,80000,OEPINT,1,Transfer completed,0,0, 0, 0, 0, 0, 0, 0,
23,10,RXFLVL,8C0080,Setup packet rec,0,0, 0, 0, 0, 0, 0, 8, 80060002 0000FF00
24,10,RXFLVL,880000,Setup comp,0,0, 0, 0, 0, 0, 0, 0,
25,80000,OEPINT,8,Setup phase done,0,80, 6, 200, 0, FF, 0, 32, 09022000 010104C0 32090400 00020806
26,40000,IEPINT,80,Transmit FIFO empty,0,0, 0, 0, 0, 0, 0, 32, 09022000 010104C0 32090400 00020806
27,40000,IEPINT,1,Transfer completed,0,0, 0, 0, 0, 0, 0, 0,
28,10,RXFLVL,850000,Out packet rec,0,0, 0, 0, 0, 0, 0, 0,
29,10,RXFLVL,870000,Transfer completed,0,0, 0, 0, 0, 0, 0, 0,
30,80000,OEPINT,1,Transfer completed,0,0, 0, 0, 0, 0, 0, 0,
31,10,RXFLVL,8C0080,Setup packet rec,0,0, 0, 0, 0, 0, 0, 8, 8006000F 0000FF00
32,10,RXFLVL,880000,Setup comp,0,0, 0, 0, 0, 0, 0, 0,
33,80000,OEPINT,8,Setup phase done,0,80, 6, F00, 0, FF, 0, 12, 050F0C00 01071002 02000000 1A030000
34,40000,IEPINT,80,Transmit FIFO empty,0,0, 0, 0, 0, 0, 0, 12, 050F0C00 01071002 02000000 1A030000
35,40000,IEPINT,1,Transfer completed,0,0, 0, 0, 0, 0, 0, 0,
36,10,RXFLVL,850000,Out packet rec,0,0, 0, 0, 0, 0, 0, 0,
37,10,RXFLVL,870000,Transfer completed,0,0, 0, 0, 0, 0, 0, 0,
38,80000,OEPINT,1,Transfer completed,0,0, 0, 0, 0, 0, 0, 0,
39,10,RXFLVL,8C0080,Setup packet rec,0,0, 0, 0, 0, 0, 0, 8, 80060303 0904FF00
40,10,RXFLVL,880000,Setup comp,0,0, 0, 0, 0, 0, 0, 0,
41,80000,OEPINT,8,Setup phase done,0,80, 6, 303, 409, FF, 0, 26, 1A033000 30003500 43003000 30003600
42,40000,IEPINT,80,Transmit FIFO empty,0,0, 0, 0, 0, 0, 0, 26, 1A033000 30003500 43003000 30003600
43,40000,IEPINT,1,Transfer completed,0,0, 0, 0, 0, 0, 0, 0,
44,10,RXFLVL,850000,Out packet rec,0,0, 0, 0, 0, 0, 0, 0,
45,10,RXFLVL,870000,Transfer completed,0,0, 0, 0, 0, 0, 0, 0,
46,80000,OEPINT,1,Transfer completed,0,0, 0, 0, 0, 0, 0, 0,
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
397,10,RXFLVL,2401F1,Out packet rec,1,0, 0, 0, 0, 0, 0, 31, 55534243 A068D0DB 08000000 80000A25
398,10,RXFLVL,260001,Transfer completed,1,0, 0, 0, 0, 0, 0, 0,
399,80000,OEPINT,1,Transfer completed,1,0, 0, 0, 0, 0, 2A, 13, 55534253 609400E2

*/

#endif
