dchwebb/Kishoof/Kishoof/src/usb/CDCHandler.cpp

#include "USB.h"
#include "CDCHandler.h"
#include "Filter.h"
#include "WaveTable.h"
#include "ExtFlash.h"
#include "Calib.h"
#include <stdio.h>
#include <charconv>

uint32_t flashBuff[8192];

// Check if a command has been received from USB, parse and action as required
void CDCHandler::ProcessCommand()
{
	if (!cmdPending) {
		return;
	}

	std::string_view cmd {comCmd};

	// Provide option to switch to USB DFU mode - this allows the MCU to be programmed with STM32CubeProgrammer in DFU mode
	if (state == serialState::dfuConfirm) {
		if (cmd.compare("y") == 0 || cmd.compare("Y") == 0) {
			usb->SendString("Switching to DFU Mode ...\r\n");
			uint32_t old = SysTickVal;
			while (SysTickVal < old + 100) {};		// Give enough time to send the message
			JumpToBootloader();
		} else {
			state = serialState::pending;
			usb->SendString("Upgrade cancelled\r\n");
		}

	} else if (state == serialState::formatConfirm) {
		if (cmd.compare("y") == 0 || cmd.compare("Y") == 0) {
			usb->SendString("Formatting flash:\r\n");
			fatTools.Format();
			usb->SendString("Restarting ...\r\n");
			uint32_t old = SysTickVal;
			while (SysTickVal < old + 100) {};		// Give enough time to send the message
			Reboot();
		} else {
			state = serialState::pending;
			usb->SendString("Format cancelled\r\n");
		}

	} else if (state == serialState::eraseConfirm) {
		if (cmd.compare("y") == 0 || cmd.compare("Y") == 0) {
			printf("Erasing flash. Please wait (slow) ...\r\n");
			extFlash.FullErase();
			printf("Flash erased\r\n");
		} else {
			state = serialState::pending;
			usb->SendString("Erase cancelled\r\n");
		}

	} else if (calib.calibrating) {						// Send command to calibration process
		calib.Calibrate(cmd[0]);

	} else if (cmd.compare("info") == 0) {				// Print diagnostic information
		extern uint32_t underrun, flashBusy;			// Diagnostics from interrupt hander and wavetable output
		printf("\r\nMountjoy Kishoof v1.0\r\n\r\n"
				"Build Date: %s %s\r\n"
				"Calibration base pitch: %.2f\r\n"
				"Calibration pitch divider: %.2f\r\n"
				"Calibration vca normal level: %d\r\n"
				"Additive wave config: %lx\r\n"
				"Config sector: %lu; address: %p\r\n"
				"Sample buffer underrun: %lu\r\n"
				"Flash busy: %lu\r\n"
				"\r\n"
				, __DATE__, __TIME__,
				calib.cfg.pitchBase,
				-1.0f / calib.cfg.pitchMult,
				calib.cfg.vcaNormal,
				wavetable.cfg.additiveWaves,
				config.currentSector,
				config.flashConfigAddr + config.currentSettingsOffset / 4,
				underrun,
				flashBusy
				);


	} else if (cmd.compare("help") == 0) {

		usb->SendString("Mountjoy Kishoof\r\n"
				"\r\nSupported commands:\r\n"
				"info        -  Show diagnostic information\r\n"
				"calib       -  Start calibration\r\n"
				"dfu         -  USB firmware upgrade\r\n"
				"wavetables  -  Print list of wavetables\r\n"
				"dirdetails  -  Print detailed FAT directory info\r\n"
				"add:XXXXXXXX   Channel B additive waves. Type 'help add' for details\r\n"
				"dispmark:X  -  CV markers in display. N - none, L - line, P - pointer\r\n"
				"clearconfig -  Erase configuration and restart\r\n"
				"saveconfig  -  Immediately save config\r\n"
				"fatinfo     -  Print fat file system details\r\n"
				"reboot      -  Reboot module\r\n"
				"\r\n"
				"Flash Tools:\r\n"
				"------------\r\n"
				"eraseflash  -  Erase all sample storage flash data\r\n"
				"format      -  Format sample storage flash\r\n"
				"fixunaligned   Attempt to fix any wavetables with Unaligned errors\r\n"
				"sreg        -  Print flash status register\r\n"
				"flashid     -  Print flash manufacturer and device IDs\r\n"
				"mem:A       -  Print 1024 bytes of flash (A = decimal address)\r\n"
				"printcluster:A Print 2048 bytes of cluster address A (>=2)\r\n"
				"clusterchain   List chain of FAT clusters\r\n"
				"cacheinfo   -  Summary of unwritten changes in header cache\r\n"
				"cachechanges   Show all bytes changed in header cache\r\n"
				"flushcache  -  Flush any changed data in cache to flash\r\n"
				"eraseblock:A   Erase block of memory (4096 bytes)\r\n"

#if (USB_DEBUG)
				"\r\n"
				"usbdebug    -  Start USB debugging\r\n"
				"\r\n"
#endif
		);

	} else if (cmd.compare("help add") == 0) {

		usb->SendString("Configure channel B additive waves\r\n"
				"syntax add:XXXXXXXX where X = 0 to 9:\r\n"
				" 0 = none\r\n"
				" 1 = fundamental sine\r\n"
				" 2 = 2nd harmonic sine\r\n"
				" 3 = 3rd harmonic sine\r\n"
				" 4 = 4th harmonic sine\r\n"
				" 5 = 5th harmonic sine\r\n"
				" 6 = 6th harmonic sine\r\n"
				" 7 = square\r\n"
				" 8 = saw tooth\r\n"
				" 9 = triangle\r\n");


#if (USB_DEBUG)
	} else if (cmd.compare("usbdebug") == 0) {				// Configure gate LED
		extern bool USBDebug;
		USBDebug = true;
		usb->SendString("Press link button to dump output\r\n");
#endif

	} else if (cmd.compare("dfu") == 0) {						// USB DFU firmware upgrade
		printf("Start DFU upgrade mode? Press 'y' to confirm.\r\n");
		state = serialState::dfuConfirm;


	} else if (cmd.compare("format") == 0) {					// Format Flash storage with FAT
		printf("Format internal storage? Press 'y' to confirm.\r\n");
		state = serialState::formatConfirm;

	} else if (cmd.compare("eraseflash") == 0) {				// Erase all flash memory
		if (!SafeMode) {
			printf("Enter safe mode first (hold encoder button whilst restarting module)\r\n");
		} else {
			printf("Erase all internal storage? Press 'y' to confirm.\r\n");
			state = serialState::eraseConfirm;
		}

	} else if (cmd.compare("reboot") == 0) {					// Reboot module
		Reboot();


	} else if (cmd.compare("calib") == 0) {						// Start calibration process
		calib.Calibrate('s');


	} else if (cmd.compare("wavetables") == 0) {				// Prints wavetable list
		printf("Num Name       Bytes    Data Bits Channels Invalid   Address    Metadata Frames\r\n");

		for (uint32_t i = 0; i < wavetable.wavetableCount; ++i) {
			printf("%3lu %8.8s %7lu %7lu %3u%1s %8u %9s %10p %08lu %6d\r\n",
					i,
					wavetable.wavList[i].name,
					wavetable.wavList[i].size,
					wavetable.wavList[i].dataSize,
					wavetable.wavList[i].byteDepth * 8,
					wavetable.wavList[i].dataFormat == 3 ? "f" : " ",	// floating point format
					wavetable.wavList[i].channels,
					wavetable.InvalidText[wavetable.wavList[i].invalid],
					wavetable.wavList[i].startAddr,
					wavetable.wavList[i].metadata,
					wavetable.wavList[i].tableCount
					);
		}
		printf("\r\n");


	} else if (cmd.compare("clearconfig") == 0) {				// Erase config from internal flash
		printf("Clearing config and restarting ...\r\n");
		config.EraseConfig();
		DelayMS(10);
		Reboot();


	} else if (cmd.compare("saveconfig") == 0) {				// Immediate config save
		config.SaveConfig(true);


	} else if (cmd.compare(0, 4, "add:") == 0) {				// configure channel B additive waves
		uint32_t val;
		auto res = std::from_chars(cmd.data() + cmd.find(":") + 1, cmd.data() + cmd.size(), val, 16);
		if (res.ec == std::errc()) {
			wavetable.cfg.additiveWaves = val;
			wavetable.CalcAdditive();
			config.ScheduleSave();
		} else {
			usb->SendString("Invalid data\r\n");
		}


	} else if (cmd.compare(0, 9, "dispmark:") == 0) {			// CV markers in display. N - none, L - line, P - pointer
		char option = cmd[9];
		if (option == 'N' || option == 'L' || option == 'P') {
			ui.cfg.displayPos = (option == 'N') ? UI::DisplayPos::off : (option == 'L') ? UI::DisplayPos::line : UI::DisplayPos::pointer;
			config.ScheduleSave();
			usb->SendString("Updated\r\n");
		} else {
			usb->SendString("Invalid data\r\n");
		}


	} else if (cmd.compare(0, 11, "eraseblock:") == 0) {		// Erase sector on external flash
		uint32_t addr;
		auto res = std::from_chars(cmd.data() + cmd.find(":") + 1, cmd.data() + cmd.size(), addr, 16);
		if (res.ec == std::errc()) {
			extFlash.BlockErase(addr);
			printf("Flash Sector Erase Address: %#010lx\r\n", addr);
		} else {
			usb->SendString("Invalid address\r\n");
		}

	} else if (cmd.compare("fixunaligned") == 0) {				// Attempt to fix unaligned wavetable headers
		wavetable.FixUnaligned();

	} else if (cmd.compare("octo") == 0) {						// Switch Flash to octal mode
		extFlash.SetOctoMode();
		printf("Changed to octal mode\r\n");

	} else if (cmd.compare("resetflash") == 0) {				// Reset Flash chip and reset to SPI mode
		extFlash.Reset();
		printf("Flash reset\r\n");

	} else if (cmd.compare("mmap") == 0) {						// Memory mapped
		extFlash.MemoryMapped();
		printf("Memory Mapped mode\r\n");

	} else if (cmd.compare("flashid") == 0) {					// External RAM ID
		uint32_t id = extFlash.GetID();
		printf("Flash ID: %#010lx\r\n", id);

	} else if (cmd.compare("chkbusy") == 0) {					// Check Flash Busy
		extFlash.CheckBusy();

	} else if (cmd.compare("wren") == 0) {						// Write Enable
		extFlash.WriteEnable();

	} else if (cmd.compare("sreg") == 0) {						// Flash Status Register
		uint32_t status = extFlash.ReadStatusReg();
		printf("Status Register: %#010lx \r\n", status);

	} else if (cmd.compare(0, 5, "mreg:") == 0) {				// Flash Register
		uint32_t addr;
		auto res = std::from_chars(cmd.data() + cmd.find(":") + 1, cmd.data() + cmd.size(), addr, 16);
		if (res.ec == std::errc()) {
			uint32_t id = extFlash.ReadReg(addr);
			printf("Flash Register: %#010lx Data: %#010lx\r\n", addr, id);
		} else {
			usb->SendString("Invalid register\r\n");
		}

	} else if (cmd.compare(0, 7, "cfgreg:") == 0) {				// Flash Cfg2 Register
		uint32_t addr;
		auto res = std::from_chars(cmd.data() + cmd.find(":") + 1, cmd.data() + cmd.size(), addr, 16);
		if (res.ec == std::errc()) {
			uint32_t id = extFlash.ReadCfgReg(addr);
			printf("Flash Register: %#010lx Data: %#010lx\r\n", addr, id);
		} else {
			usb->SendString("Invalid register\r\n");
		}

	} else if (cmd.compare(0, 5, "rmem:") == 0) {				// Read Memory
		uint32_t addr;
		auto res = std::from_chars(cmd.data() + cmd.find(":") + 1, cmd.data() + cmd.size(), addr, 16);
		if (res.ec == std::errc()) {
			uint32_t val = extFlash.Read(addr);
			printf("Flash Data Address: %#010lx Data: %#010lx\r\n", addr, val);
		} else {
			usb->SendString("Invalid address\r\n");
		}

	} else if (cmd.compare(0, 5, "wmem:") == 0) {				// Write Memory Page with test data
		uint32_t addr;
		auto res = std::from_chars(cmd.data() + cmd.find(":") + 1, cmd.data() + cmd.size(), addr, 16);
		if (res.ec == std::errc()) {			// no error
			// Create test buffer
			uint32_t testBuffer[64];
			for (uint32_t i = 0; i < 64; ++i) {
				testBuffer[i] = i;
			}
			extFlash.WriteData(addr, testBuffer, 64);
			printf("Write Address: %#010lx\r\n", addr);
		} else {
			usb->SendString("Invalid address\r\n");
		}


	//--------------------------------------------------------------------------------------------------
	// All flash commands that rely on memory mapped data to follow this guard
	} else if (extFlash.flashCorrupt) {
		printf("** Flash Corrupt **\r\n");

	} else if (cmd.compare("fatinfo") == 0) {					// Get basic FAT directory list
		fatTools.PrintFatInfo();

	} else if (cmd.compare("dir") == 0) {						// Get basic FAT directory list
		if (fatTools.noFileSystem) {
			printf("** No file System **\r\n");
		} else {
			char workBuff[256];
			strcpy(workBuff, "/");

			fatTools.InvalidateFatFSCache();					// Ensure that the FAT FS cache is updated
			fatTools.PrintFiles(workBuff);
		}

	} else if (cmd.compare("dirdetails") == 0) {				// Get detailed FAT directory info
		fatTools.PrintDirInfo();


	} else if (cmd.compare("clusterchain") == 0) {				// Print used clusters with links from FAT area
		printf("Cluster | Link\r\n");
		uint32_t cluster = 0;
		while (fatTools.clusterChain[cluster]) {
			printf("%7lu   0x%04x\r\n", cluster, fatTools.clusterChain[cluster]);
			++cluster;
		}


	} else if (cmd.compare("cacheinfo") == 0) {				// Basic counts of differences between cache and Flash
		for (uint32_t blk = 0; blk < (fatCacheSectors / fatEraseSectors); ++blk) {

			// Check if block is actually dirty or clean
			uint32_t dirtyBytes = 0, firstDirtyByte = 0, lastDirtyByte = 0;
			for (uint32_t byte = 0; byte < (fatEraseSectors * fatSectorSize); ++byte) {
				uint32_t offset = (blk * fatEraseSectors * fatSectorSize) + byte;
				if (fatTools.headerCache[offset] != flashAddress[offset]) {
					++dirtyBytes;
					if (firstDirtyByte == 0) {
						firstDirtyByte = offset;
					}
					lastDirtyByte = offset;
				}
			}

			const bool blockDirty = (fatTools.dirtyCacheBlocks & (1 << blk));
			printf("Block %2lu: %s  Dirty bytes: %lu from %lu to %lu\r\n",
					blk, (blockDirty ? "dirty" : "     "), dirtyBytes, firstDirtyByte, lastDirtyByte);
		}

		// the write cache holds any blocks currently being written to to avoid multiple block erasing when writing large data
		if (fatTools.writeCacheDirty) {
			uint32_t dirtyBytes = 0, firstDirtyByte = 0, lastDirtyByte = 0;
			for (uint32_t byte = 0; byte < (fatEraseSectors * fatSectorSize); ++byte) {
				uint32_t offset = (fatTools.writeBlock * fatEraseSectors * fatSectorSize) + byte;
				if (fatTools.writeBlockCache[byte] != flashAddress[offset]) {
					++dirtyBytes;
					if (firstDirtyByte == 0) {
						firstDirtyByte = offset;
					}
					lastDirtyByte = offset;
				}
			}

			printf("Block %2lu: %s  Dirty bytes: %lu from %lu to %lu\r\n",
					fatTools.writeBlock, (fatTools.writeCacheDirty ? "dirty" : "     "), dirtyBytes, firstDirtyByte, lastDirtyByte);

		}


	} else if (cmd.compare("cachechanges") == 0) {			// List bytes that are different in cache to Flash
		uint32_t count = 0;
		uint8_t oldCache = 0, oldFlash = 0;
		bool skipDuplicates = false;

		for (uint32_t i = 0; i < (fatCacheSectors * fatSectorSize); ++i) {

			if (flashAddress[i] != fatTools.headerCache[i]) {					// Data has changed
				if (oldCache == fatTools.headerCache[i] && oldFlash == flashAddress[i] && i > 0) {
					if (!skipDuplicates) {
						printf("...\r\n");						// Print continuation mark
						skipDuplicates = true;
					}
				} else {
					printf("%5lu c: 0x%02x f: 0x%02x\r\n", i, fatTools.headerCache[i], flashAddress[i]);
				}

				oldCache = fatTools.headerCache[i];
				oldFlash = flashAddress[i];
				++count;
			} else {
				if (skipDuplicates) {
					printf("%5lu c: 0x%02x f: 0x%02x\r\n", i - 1, oldCache, oldFlash);
					skipDuplicates = false;
				}
			}

		}
		printf("Found %lu different bytes\r\n", count);


	} else if (cmd.compare("flushcache") == 0) {				// Flush FAT cache to Flash
		const uint8_t sectors = fatTools.FlushCache();
		printf("%i blocks flushed\r\n", sectors);
		extFlash.MemoryMapped();


	} else if (cmd.compare(0, 5, "write") == 0) {				// Write test pattern to flash writeA:W [A = address; W = num words]
		const int32_t address = ParseInt(cmd, 'e', 0, 0xFFFFFF);
		if (address >= 0) {
			const uint32_t words = ParseInt(cmd, ':');
			printf("Writing %ld words to %ld ...\r\n", words, address);

			for (uint32_t a = 0; a < words; ++a) {
				flashBuff[a] = a + 1;
			}
			extFlash.WriteData(address, flashBuff, words);

			extFlash.MemoryMapped();
			printf("Finished\r\n");

		}


	} else if (cmd.compare(0, 4, "mem:") == 0) {					// Flash: print 1024 words of memory mapped data
		const int32_t address = ParseInt(cmd, ':', 0, 0xFFFFFF);
		if (address >= 0) {
			const uint32_t* p = (uint32_t*)(0x90000000 + address);

			for (uint32_t a = 0; a < 256; a += 4) {
				printf("%6ld: %#010lx %#010lx %#010lx %#010lx\r\n", (a * 4) + address, p[a], p[a + 1], p[a + 2], p[a + 3]);
			}
		}
		printf("\r\n");

	} else if (cmd.compare(0, 13, "printcluster:") == 0) {			// Flash: print 4096 words memory mapped data
		const int32_t cluster = ParseInt(cmd, ':', 2, 0xFFFFFF);
		if (cluster >= 2) {
			printf("Cluster %ld:\r\n", cluster);

			const uint32_t* p = (uint32_t*)(fatTools.GetClusterAddr(cluster, true));

			for (uint32_t a = 0; a < 1024; a += 4) {
				printf("0x%08lx: %#010lx %#010lx %#010lx %#010lx\r\n", (a * 4) + (uint32_t)p, p[a], p[a + 1], p[a + 2], p[a + 3]);
			}
		}

	} else if (cmd.compare(0, 11, "printblock:") == 0) {			// Flash prints cluster with minimal text for automated debugging
		const int32_t block = ParseInt(cmd, ':', 0, 0xFFFFFF);
		if (block >= 0) {
			printf("Block %ld:\n", block);

			const uint32_t* p = (uint32_t*)(flashAddress + block * fatClusterSize);

			for (uint32_t a = 0; a < 1024; a += 4) {
				printf("%08lx %08lx %08lx %08lx\n", p[a], p[a + 1], p[a + 2], p[a + 3]);
			}
		}

	} else {
		printf("Unrecognised command: %s\r\nType 'help' for supported commands\r\n", cmd.data());
	}

	cmdPending = false;
}


void CDCHandler::DataIn()
{
	if (inBuffSize > 0 && inBuffSize % USB::ep_maxPacket == 0) {
		inBuffSize = 0;
		EndPointTransfer(Direction::in, inEP, 0);				// Fixes issue transmitting an exact multiple of max packet size (n x 64)
	}
}


// As this is called from an interrupt assign the command to a variable so it can be handled in the main loop
void CDCHandler::DataOut()
{
	// Check if sufficient space in command buffer
	const uint32_t newCharCnt = std::min(outBuffCount, maxCmdLen - 1 - buffPos);

	strncpy(&comCmd[buffPos], (char*)outBuff, newCharCnt);
	buffPos += newCharCnt;

	// Check if cr has been sent yet
	if (comCmd[buffPos - 1] == 13 || comCmd[buffPos - 1] == 10 || buffPos == maxCmdLen - 1) {
		comCmd[buffPos - 1] = '\0';
		cmdPending = true;
		buffPos = 0;
	}
}


void CDCHandler::ActivateEP()
{
	EndPointActivate(USB::CDC_In,   Direction::in,  EndPointType::Bulk);			// Activate CDC in endpoint
	EndPointActivate(USB::CDC_Out,  Direction::out, EndPointType::Bulk);			// Activate CDC out endpoint
	EndPointActivate(USB::CDC_Cmd,  Direction::in,  EndPointType::Interrupt);		// Activate Command IN EP

	EndPointTransfer(Direction::out, outEP, USB::ep_maxPacket);
}


void CDCHandler::ClassSetup(usbRequest& req)
{
	if (req.RequestType == DtoH_Class_Interface && req.Request == GetLineCoding) {
		SetupIn(req.Length, (uint8_t*)&lineCoding);
	}

	if (req.RequestType == HtoD_Class_Interface && req.Request == SetLineCoding) {
		// Prepare to receive line coding data in ClassSetupData
		usb->classPendingData = true;
		EndPointTransfer(Direction::out, 0, req.Length);
	}
}


void CDCHandler::ClassSetupData(usbRequest& req, const uint8_t* data)
{
	// ClassSetup passes instruction to set line coding - this is the data portion where the line coding is transferred
	if (req.RequestType == HtoD_Class_Interface && req.Request == SetLineCoding) {
		lineCoding = *(LineCoding*)data;
	}
}

int32_t CDCHandler::ParseInt(const std::string_view cmd, const char precedingChar, const int32_t low, const int32_t high) {
	int32_t val = -1;
	const int8_t pos = cmd.find(precedingChar);		// locate position of character preceding
	if (pos >= 0 && std::strspn(&cmd[pos + 1], "0123456789-") > 0) {
		val = std::stoi(&cmd[pos + 1]);
	}
	if (high > low && (val > high || val < low)) {
		printf("Must be a value between %ld and %ld\r\n", low, high);
		return low - 1;
	}
	return val;
}


float CDCHandler::ParseFloat(const std::string_view cmd, const char precedingChar, const float low = 0.0f, const float high = 0.0f) {
	float val = -1.0f;
	const int8_t pos = cmd.find(precedingChar);		// locate position of character preceding
	if (pos >= 0 && std::strspn(&cmd[pos + 1], "0123456789.") > 0) {
		val = std::stof(&cmd[pos + 1]);
	}
	if (high > low && (val > high || val < low)) {
		printf("Must be a value between %f and %f\r\n", low, high);
		return low - 1.0f;
	}
	return val;
}


// Descriptor definition here as requires constants from USB class
const uint8_t CDCHandler::Descriptor[] = {
	// IAD Descriptor - Interface association descriptor for CDC class
	0x08,									// bLength (8 bytes)
	USB::IadDescriptor,						// bDescriptorType
	USB::CDCCmdInterface,					// bFirstInterface
	0x02,									// bInterfaceCount
	0x02,									// bFunctionClass (Communications and CDC Control)
	0x02,									// bFunctionSubClass
	0x01,									// bFunctionProtocol
	USB::CommunicationClass,				// String Descriptor

	// Interface Descriptor
	0x09,									// bLength: Interface Descriptor size
	USB::InterfaceDescriptor,				// bDescriptorType: Interface
	USB::CDCCmdInterface,					// bInterfaceNumber: Number of Interface
	0x00,									// bAlternateSetting: Alternate setting
	0x01,									// bNumEndpoints: 1 endpoint used
	0x02,									// bInterfaceClass: Communication Interface Class
	0x02,									// bInterfaceSubClass: Abstract Control Model
	0x01,									// bInterfaceProtocol: Common AT commands
	USB::CommunicationClass,				// iInterface

	// Header Functional Descriptor
	0x05,									// bLength: Endpoint Descriptor size
	USB::ClassSpecificInterfaceDescriptor,	// bDescriptorType: CS_INTERFACE
	0x00,									// bDescriptorSubtype: Header Func Desc
	0x10,									// bcdCDC: spec release number
	0x01,

	// Call Management Functional Descriptor
	0x05,									// bFunctionLength
	USB::ClassSpecificInterfaceDescriptor,	// bDescriptorType: CS_INTERFACE
	0x01,									// bDescriptorSubtype: Call Management Func Desc
	0x00,									// bmCapabilities: D0+D1
	0x01,									// bDataInterface: 1

	// ACM Functional Descriptor
	0x04,									// bFunctionLength
	USB::ClassSpecificInterfaceDescriptor,	// bDescriptorType: CS_INTERFACE
	0x02,									// bDescriptorSubtype: Abstract Control Management desc
	0x02,									// bmCapabilities

	// Union Functional Descriptor
	0x05,									// bFunctionLength
	USB::ClassSpecificInterfaceDescriptor,	// bDescriptorType: CS_INTERFACE
	0x06,									// bDescriptorSubtype: Union func desc
	0x00,									// bMasterInterface: Communication class interface
	0x01,									// bSlaveInterface0: Data Class Interface

	// Endpoint 2 Descriptor
	0x07,									// bLength: Endpoint Descriptor size
	USB::EndpointDescriptor,				// bDescriptorType: Endpoint
	USB::CDC_Cmd,							// bEndpointAddress
	USB::Interrupt,							// bmAttributes: Interrupt
	0x08,									// wMaxPacketSize
	0x00,
	0x10,									// bInterval

	//---------------------------------------------------------------------------

	// Data class interface descriptor
	0x09,									// bLength: Endpoint Descriptor size
	USB::InterfaceDescriptor,				// bDescriptorType:
	USB::CDCDataInterface,					// bInterfaceNumber: Number of Interface
	0x00,									// bAlternateSetting: Alternate setting
	0x02,									// bNumEndpoints: Two endpoints used
	0x0A,									// bInterfaceClass: CDC
	0x00,									// bInterfaceSubClass:
	0x00,									// bInterfaceProtocol:
	0x00,									// iInterface:

	// Endpoint OUT Descriptor
	0x07,									// bLength: Endpoint Descriptor size
	USB::EndpointDescriptor,				// bDescriptorType: Endpoint
	USB::CDC_Out,							// bEndpointAddress
	USB::Bulk,								// bmAttributes: Bulk
	LOBYTE(USB::ep_maxPacket),				// wMaxPacketSize:
	HIBYTE(USB::ep_maxPacket),
	0x00,									// bInterval: ignore for Bulk transfer

	// Endpoint IN Descriptor
	0x07,									// bLength: Endpoint Descriptor size
	USB::EndpointDescriptor,				// bDescriptorType: Endpoint
	USB::CDC_In,							// bEndpointAddress
	USB::Bulk,								// bmAttributes: Bulk
	LOBYTE(USB::ep_maxPacket),				// wMaxPacketSize:
	HIBYTE(USB::ep_maxPacket),
	0x00,									// bInterval: ignore for Bulk transfer
};


uint32_t CDCHandler::GetInterfaceDescriptor(const uint8_t** buffer) {
	*buffer = Descriptor;
	return sizeof(Descriptor);
}
