dchwebb/Kishoof/Kishoof/src/usb/CDCHandler.h

#pragma once

#include "initialisation.h"
#include "USBHandler.h"
#include <string>


class USB;

class CDCHandler : public USBHandler {
public:
	CDCHandler(USB* usb, uint8_t inEP, uint8_t outEP, int8_t interface) : USBHandler(usb, inEP, outEP, interface) {
		outBuff = xfer_buff;
	}

	void DataIn() override;
	void DataOut() override;
	void ActivateEP() override;
	void ClassSetup(usbRequest& req) override;
	void ClassSetupData(usbRequest& req, const uint8_t* data) override;
	uint32_t GetInterfaceDescriptor(const uint8_t** buffer) override;
	int32_t ParseInt(const std::string_view cmd, const char precedingChar, const int32_t low = 0, const int32_t high = 0);

	void ProcessCommand();			// Processes command received during interrupt

	bool cmdPending = false;
	static constexpr uint32_t maxCmdLen = 40;
	char comCmd[maxCmdLen];


	struct LineCoding {
		uint32_t bitrate;    		// Data terminal rate in bits per sec.
		uint8_t format;      		// Stop Bits: 0-1 Stop Bit; 1-1.5 Stop Bits; 2-2 Stop Bits
		uint8_t paritytype;  		// Parity: 0 = None; 1 = Odd; 2 = Even; 3 = Mark; 4 = Space; 6 bDataBits 1 Data bits
		uint8_t datatype;    		// Data bits (5, 6, 7,	8 or 16)
	} lineCoding;
private:
	enum {SetLineCoding = 0x20, GetLineCoding = 0x21};						// See CDC documentation rev 1.2 p.30
	enum {HtoD_Class_Interface = 0x21, DtoH_Class_Interface = 0xA1};		// A1 = [1|01|00001] Device to host | Class | Interface;
	uint32_t xfer_buff[64];
	uint32_t buffPos = 0;

	// State machine for multi-stage commands
	enum class serialState {pending, dfuConfirm, formatConfirm, eraseConfirm, calibConfirm};
	serialState state = serialState::pending;

	static const uint8_t Descriptor[];

	float ParseFloat(const std::string_view cmd, const char precedingChar, const float low, const float high);
};
